usnistgov/UAS-6.0-First-Responder-UAS-Wireless-Data-Gatherer-Challenge/pics/FoxNode_disp1.jpg

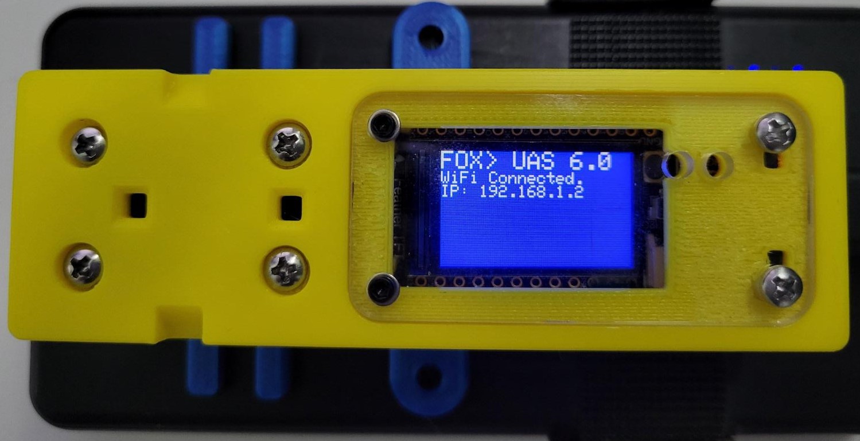
pics/FoxNode_disp1.jpg
