usnistgov/UAS-6.0-First-Responder-UAS-Wireless-Data-Gatherer-Challenge/pics/FoxNode_Fully_Connected.jpg

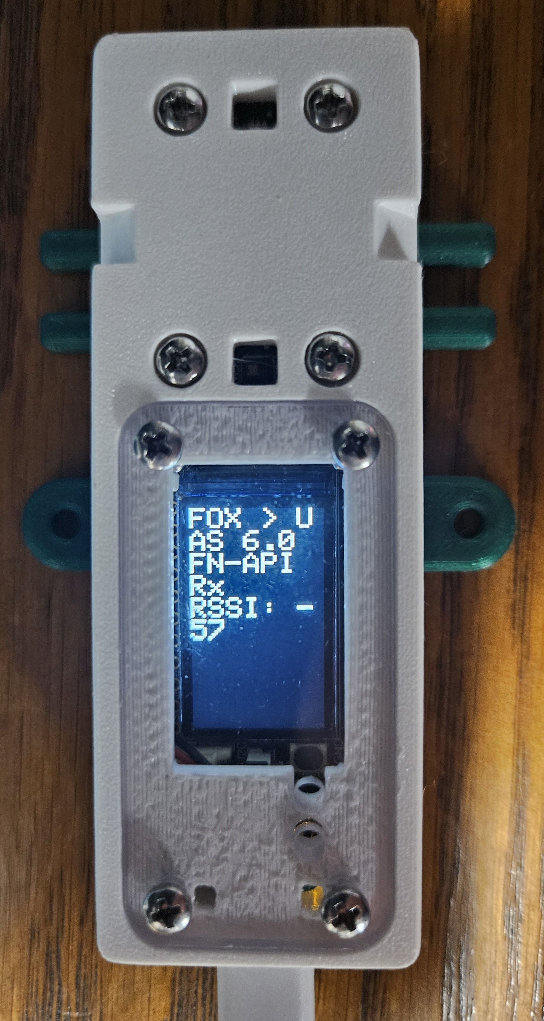
pics/FoxNode_Fully_Connected.jpg
