usnistgov/UAS-6.0-First-Responder-UAS-Wireless-Data-Gatherer-Challenge/pics/FoxNode_StateDiagram_Stage3.png

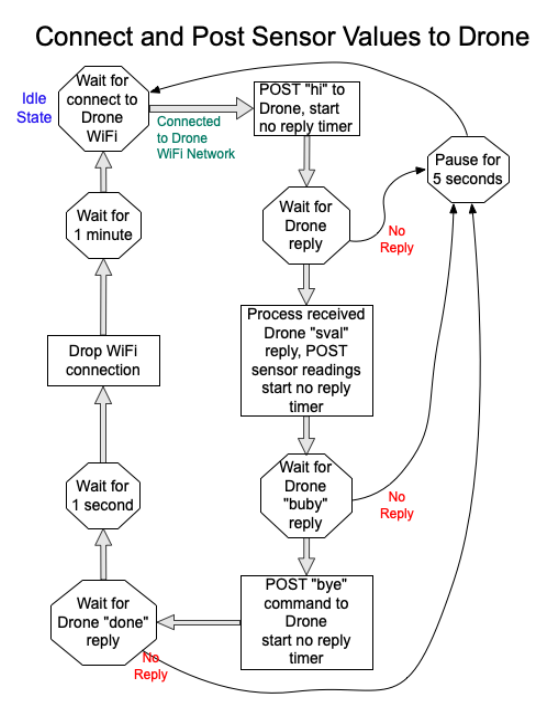
pics/FoxNode_StateDiagram_Stage3.png
