usnistgov/UAS-6.0-First-Responder-UAS-Wireless-Data-Gatherer-Challenge/stage3_foxnode/live_event_datasets/Test1/Engineering_Dynamics_Test1/Screenshot 2025-04-08 134028_ Pretty Print.png

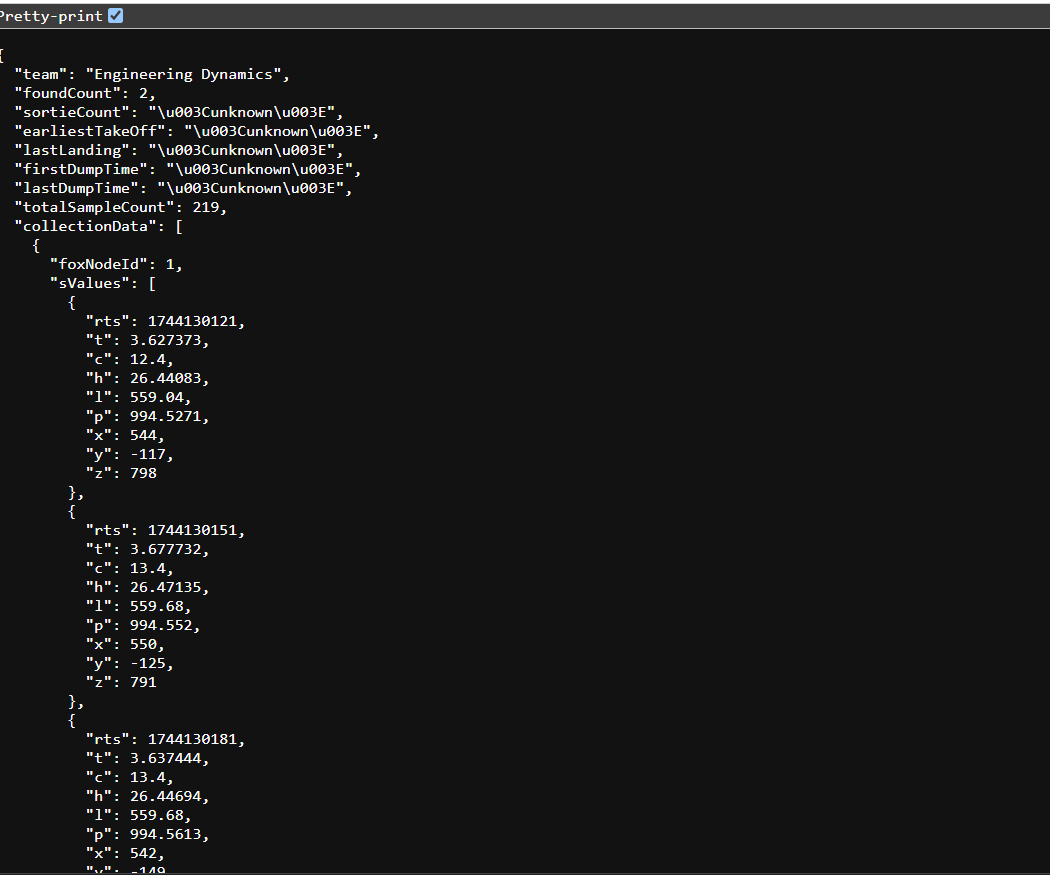
stage3_foxnode/live_event_datasets/Test1/Engineering_Dynamics_Test1/Screenshot 2025-04-08 134028_ Pretty Print.png
