usnistgov/UAS-6.0-First-Responder-UAS-Wireless-Data-Gatherer-Challenge/stage3_foxnode/live_event_datasets/Test2/Flyt_Test2/Flyt test 2.txt

{
  "bigDump": {
    "team": "Flyt",
    "foundCount": 22,
    "sortieCount": 1,
    "earliestTakeOff": 1744142474,
    "lastLanding": 1744142474,
    "firstDumpTime": 1744142475,
    "lastDumpTime": 1744144449,
    "totalSampleCount": 2008,
    "collectData": [
      {
        "foxNodeId": 5,
        "sValues": [
          {
            "t": 21.53353,
            "c": 25.7,
            "h": 37.29305,
            "l": 15892.48,
            "p": 994.1738,
            "x": 0,
            "y": 91,
            "z": 1067,
            "lat": 64.83,
            "lon": -147.77,
            "elev": 137,
            "ts": 1744142336
          },
          {
            "t": 22.27878,
            "c": 23.7,
            "h": 37.74472,
            "l": 15856.64,
            "p": 994.158,
            "x": 13,
            "y": 85,
            "z": 1015,
            "lat": 64.83,
            "lon": -147.77,
            "elev": 137,
            "ts": 1744142366
          },
          {
            "t": 22.71184,
            "c": 30.7,
            "h": 38.00717,
            "l": 15836.16,
            "p": 994.1506,
            "x": 5,
            "y": 108,
            "z": 1005,
            "lat": 64.83,
            "lon": -147.77,
            "elev": 137,
            "ts": 1744142396
          },
          {
            "t": 23.07439,
            "c": 34.7,
            "h": 38.2269,
            "l": 15897.6,
            "p": 994.1365,
            "x": -4,
            "y": 78,
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
            "lon": -85.53937,
            "elev": 226.0727,
            "ts": 3155791106
          },
          {
            "t": 9.649805,
            "c": 29.8,
            "h": 30.09079,
            "l": 1562.24,
            "p": 994.125,
            "x": -48,
            "y": -69,
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
