usnistgov/UAS-6.0-First-Responder-UAS-Wireless-Data-Gatherer-Challenge/stage3_foxnode/live_event_datasets/Test1/Flyt_Test1/Screenshot 2025-04-08 092909.png

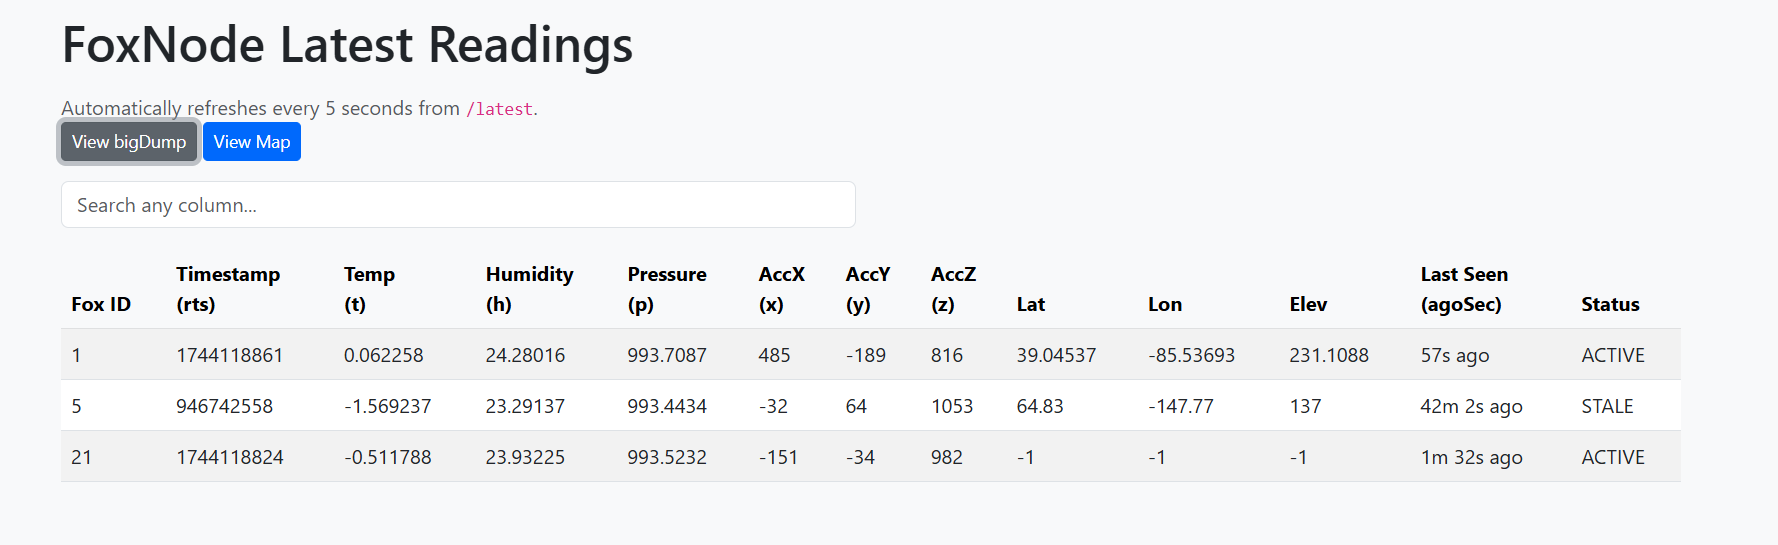
stage3_foxnode/live_event_datasets/Test1/Flyt_Test1/Screenshot 2025-04-08 092909.png
