usnistgov/UAS-6.0-First-Responder-UAS-Wireless-Data-Gatherer-Challenge/stage3_foxnode/live_event_datasets/Test1/Flyt_Test1/Test 1 bucket photos/1A.jpg

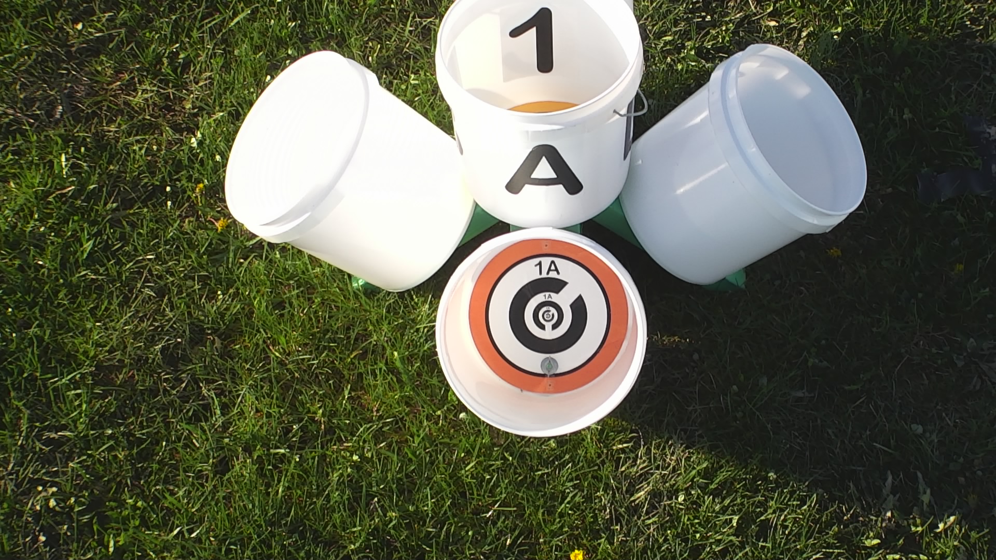
stage3_foxnode/live_event_datasets/Test1/Flyt_Test1/Test 1 bucket photos/1A.jpg
