usnistgov/UAS-6.0-First-Responder-UAS-Wireless-Data-Gatherer-Challenge/stage3_foxnode/live_event_datasets/Test1/UFRTC_Test1/Macro Map Screenshot- Patrick Request.png

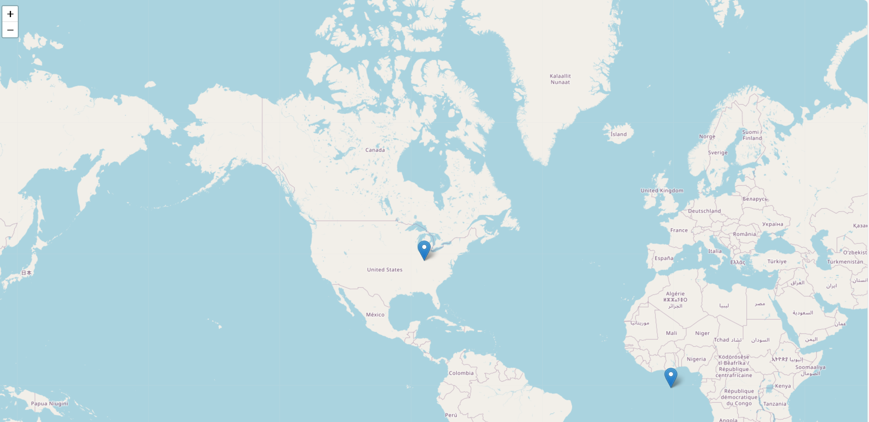
stage3_foxnode/live_event_datasets/Test1/UFRTC_Test1/Macro Map Screenshot- Patrick Request.png
