usnistgov/UAS-6.0-First-Responder-UAS-Wireless-Data-Gatherer-Challenge/stage3_foxnode/live_event_datasets/Test2/Engineering_Dynamics_Test2/NIST Server Raw.png

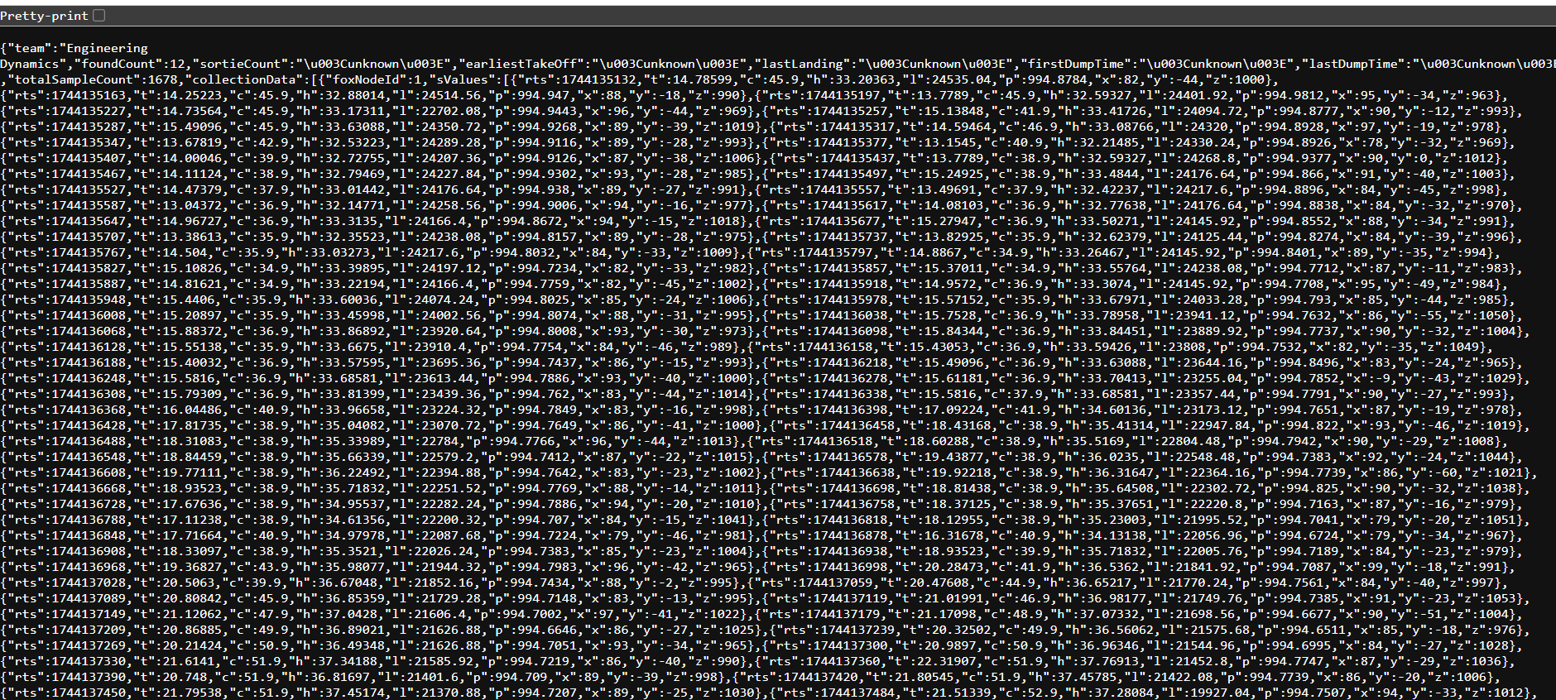
stage3_foxnode/live_event_datasets/Test2/Engineering_Dynamics_Test2/NIST Server Raw.png
