usnistgov/UAS-6.0-First-Responder-UAS-Wireless-Data-Gatherer-Challenge/stage3_foxnode/live_event_datasets/Test3/Team 7 Engineering Dynamics Test 3/RF GUI.png

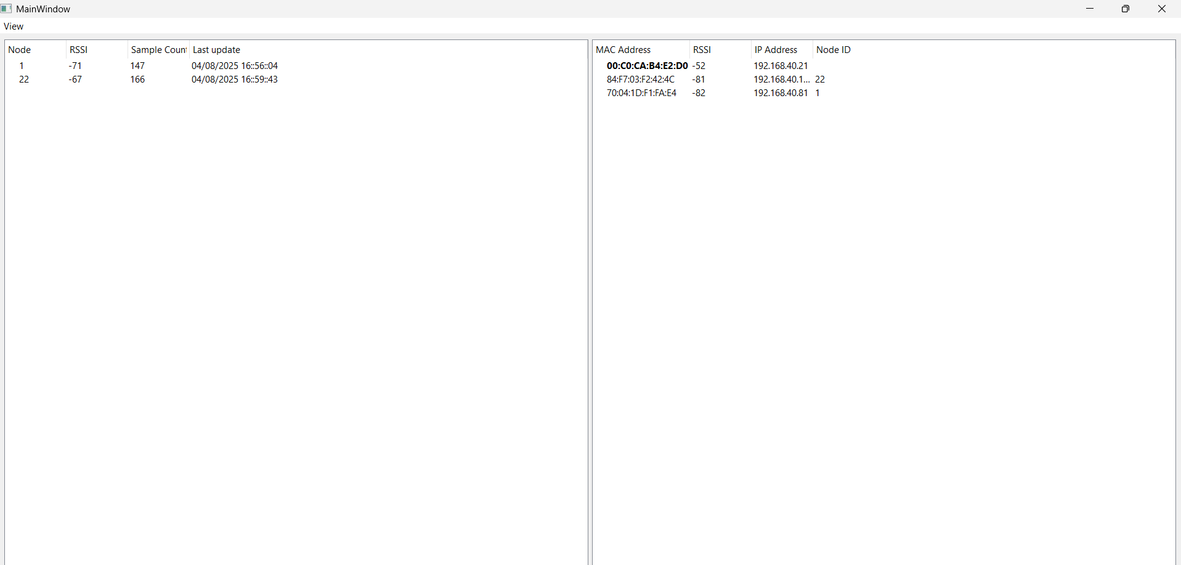
stage3_foxnode/live_event_datasets/Test3/Team 7 Engineering Dynamics Test 3/RF GUI.png
