usnistgov/UAS-6.0-First-Responder-UAS-Wireless-Data-Gatherer-Challenge/stage3_foxnode/live_event_datasets/Test4/Engineering_Dyanmics_Test4/Sensor Map.png

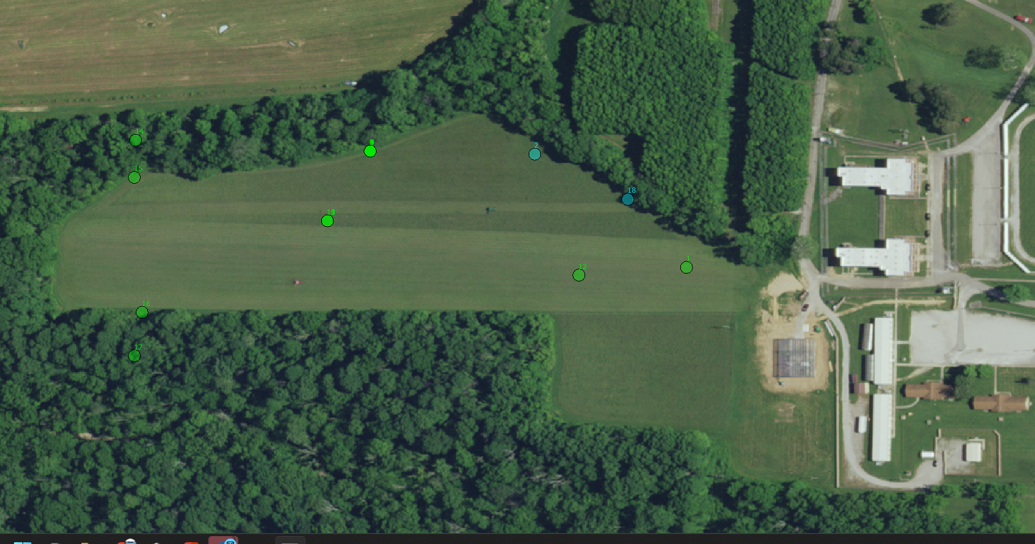
stage3_foxnode/live_event_datasets/Test4/Engineering_Dyanmics_Test4/Sensor Map.png
