usnistgov/UAS-6.0-First-Responder-UAS-Wireless-Data-Gatherer-Challenge/stage3_foxnode/live_event_datasets/Test4/Flyt_Test4/Screenshot 2025-04-09 100819.png

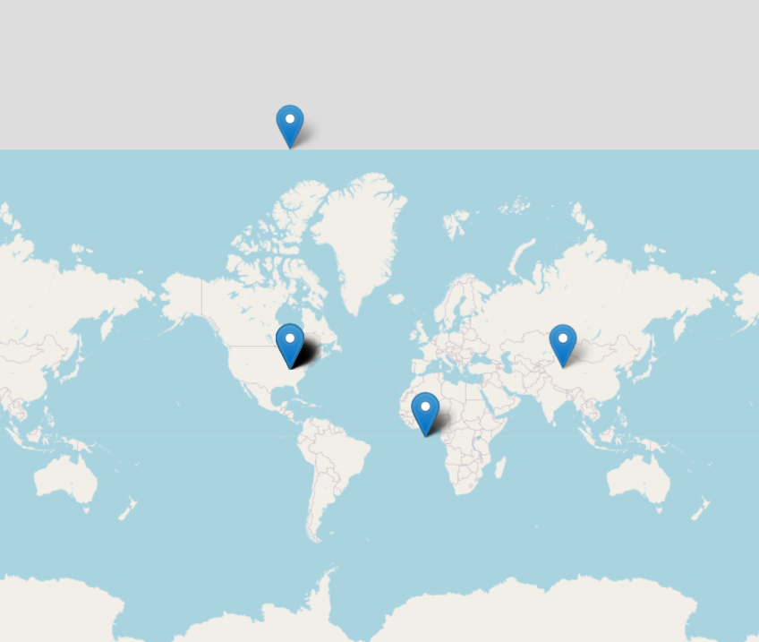
stage3_foxnode/live_event_datasets/Test4/Flyt_Test4/Screenshot 2025-04-09 100819.png
