usnistgov/UAS-6.0-First-Responder-UAS-Wireless-Data-Gatherer-Challenge/stage3_foxnode/live_event_datasets/Test4/Flyt_Test4/target_photos/DJI_0039.jpg

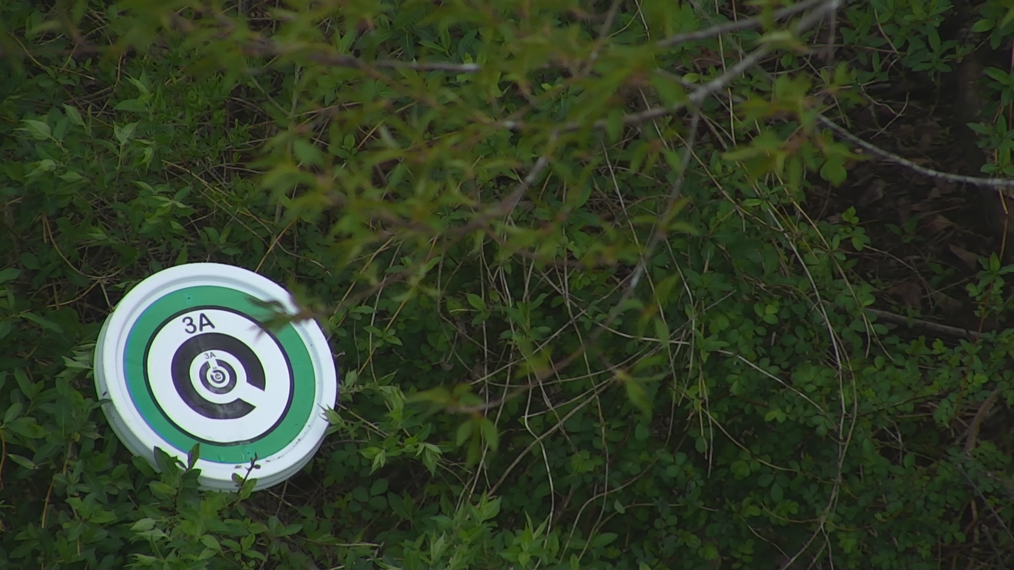
stage3_foxnode/live_event_datasets/Test4/Flyt_Test4/target_photos/DJI_0039.jpg
