usnistgov/UAS-6.0-First-Responder-UAS-Wireless-Data-Gatherer-Challenge/stage3_foxnode/live_event_datasets/Test4/UFRTC_Test4/GeoSensorData.png

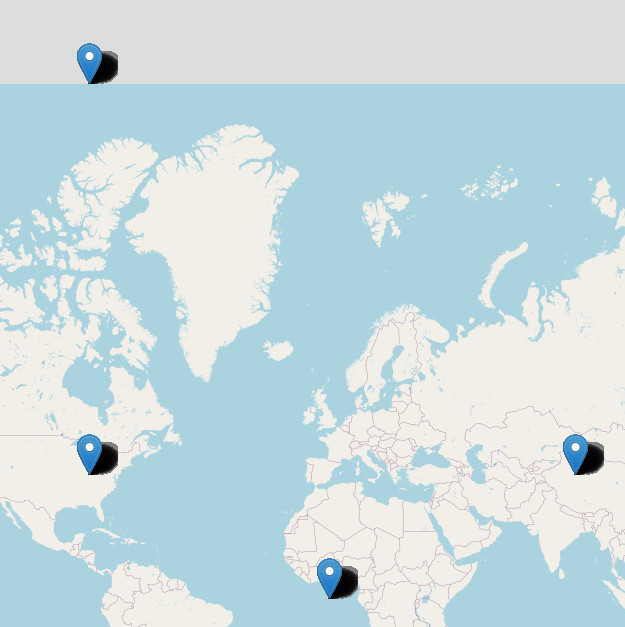
stage3_foxnode/live_event_datasets/Test4/UFRTC_Test4/GeoSensorData.png
