usnistgov/UAS-6.0-First-Responder-UAS-Wireless-Data-Gatherer-Challenge/stage3_foxnode/live_event_datasets/Test4/UFRTC_Test4/Target_Photos/DJI_20250408151507_0001_T.JPG

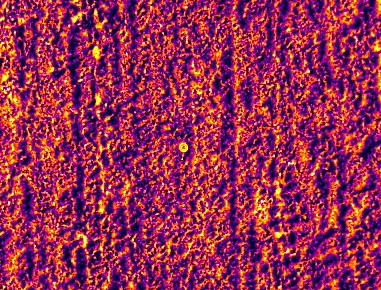
stage3_foxnode/live_event_datasets/Test4/UFRTC_Test4/Target_Photos/DJI_20250408151507_0001_T.JPG
