usnistgov/UAS-6.0-First-Responder-UAS-Wireless-Data-Gatherer-Challenge/foxnode/stateMachine/display.cpp

#include "display.h"
#include "httpComms.h"


// Compile-time guard: PSKs must never be displayed.
// If any PSK macros are present and you try to compile display.cpp, fail the build.
#if (FOXNODE_ALLOW_DISPLAY_PSK == 0)
  #if defined(WIFI_PASSWORD) || defined(NTP_WIFI_PASSWORD)
    #error "display.cpp must not reference WIFI_PASSWORD or NTP_WIFI_PASSWORD. Remove PSK display and use secrets/NVS."
  #endif
#endif

// Helper: print SSID and provisioning indicator without ever displaying PSK.
static void tftPrintSSIDLine(const char *label, WifiProfile profile) {
  String ssid;
  String throwawayPsk;  // required by secretsGetWiFi signature; do NOT display it

  bool ok = secretsGetWiFi(profile, ssid, throwawayPsk);
  tft.print(label);
  if (ok) {
    tft.print(ssid);
    tft.print("  PROV: YES");
  } else {
    tft.print("<not provisioned>  PROV: NO");
  }
  tft.println();
}

Adafruit_ST7789 tft = Adafruit_ST7789(TFT_CS, TFT_DC, TFT_RST);                          // Use dedicated hardware SPI pins for TFT disp

short disp_rotation = 3;			                                                           // Set display initial rotation TFT display: input "1" through "4"

// NOTE The RTC is on the sensor board, but this f() deals with printing.
void RTC_tftPrint() {                                                                    // TFT-display time as a formatted string (ISO 8601)
  tft.setTextSize(2);
  tft.setTextColor(ST77XX_WHITE);
  char formattedTime[20];
  snprintf(formattedTime, sizeof(formattedTime), "%04d-%02d-%02d %02d:%02d:%02d",
           myTime.tm_year + 1900, myTime.tm_mon + 1, myTime.tm_mday,
           myTime.tm_hour, myTime.tm_min, myTime.tm_sec);
  tft.println(formattedTime);
}

void tft_display(int disp_update) {
  //disp key 
  //5 - NTP Setup/Info               (YELLOW) 
  //4 - on rx HTTP update param"     (BLACK)
  //3 - on sent POST                 (GREEN)
  //2 - no connection to HTTP server (ORANGE)
  //1 - On WiFi got IP               (BLUE) 
  //0 - TFT init code                (GREEN)
  wantToPaintDisplay = 0;			// clear any pending request to paint the display
  if (disp_update == 5) {           // (YELLOW) disp FN NTP time setting 
    tft.setRotation(disp_rotation);tft.fillScreen(ST77XX_YELLOW);tft.setCursor(0, 0);
    tft.setTextSize(3);tft.setTextColor(ST77XX_WHITE);tft.println("FOX > UAS 6.0");
    tft.setTextSize(2);tft.print("FoxID: ");tft.println(thisFoxNodeId);
    tft.setTextSize(2);tft.println("NTP connect...");
    // Display SSID only (never PSK). Pulled from NVS.
    tftPrintSSIDLine("SSID: ", WifiProfile::NTP);
  } else if (disp_update == 4) {    // (BLACK) display is built in, ST7789 (TFT display) 240x135
    tft.setRotation(disp_rotation);pinMode(TFT_BACKLITE, OUTPUT);digitalWrite(TFT_BACKLITE, HIGH);tft.init(135, 240);
    tft.setCursor(0, 0);tft.fillScreen(ST77XX_BLACK);tft.setTextSize(3);tft.setTextColor(ST77XX_WHITE); // End TFT init
    tft.println("FOX > UAS 6.0");tft.println("FN-API Rx");tft.setTextSize(2);                      
  }else if (disp_update == 3) {     // (GREEN)
    tft.setRotation(disp_rotation);tft.fillScreen(ST77XX_GREEN);
    //tft.setCursor(0, 0);tft.setTextSize(2);tft.setTextColor(ST77XX_WHITE);tft.println("FOX > UAS 6.0");
    tft.setCursor(0, 0);RTC_tftPrint();  // Display formatted RTC time info
    tft.setTextSize(2);tft.setTextColor(ST77XX_RED);
    tft.print("FoxID: ");tft.println(thisFoxNodeId);
    tft.print("IP: ");tft.println(WiFi.localIP());
    tft.print("RSSI: ");tft.println(String(data_doc["rssi"]));			// This is what has been pushed to the Ringbuffer and will be POSTED when UAS connects
    tft.print("STA_TX_PWR: ");tft.println(String(data_doc["tpwr"]));
    tft.print("S:");tft.println(UAS_Server_IP);
    tft.print("HTTP Resp: ");
    if (httpResponseCode == -999) {tft.println("N/A");}
    else {tft.println(httpResponseCode);}
    tft.print("TLS: ");
    if (tlsState == TLS_STATE_OK) {
      tft.println("OK");
    } else if (tlsState == TLS_STATE_FAIL) {
      tft.println("FAIL");
      if (tlsLastError[0]) {
        // Keep it readable on the TFT by shrinking the font for the error snippet.
        tft.setTextSize(1);
        tft.println(tlsLastError);
        tft.setTextSize(2);
      }
    } else {
      tft.println("N/A");
    }

    tft.setTextColor(ST77XX_WHITE);										// Set back to white for later calls
  } else if (disp_update == 2) {      // (ORANGE) no WiFi/HTTP Server connection available 
    tft.setRotation(disp_rotation);tft.fillScreen(ST77XX_ORANGE);tft.setCursor(0, 0);tft.setTextSize(3);tft.setTextColor(ST77XX_WHITE);
    tft.println(("FOX > UAS 6.0"));tft.setTextSize(2);
    RTC_tftPrint();
    tft.print("FoxID: ");tft.println(thisFoxNodeId);
    tft.println("Looking for Network");
    // Display SSID only (never PSK). Pulled from NVS.
    tftPrintSSIDLine("SSID: ", WifiProfile::UAS6);
    tft.println(UAS_Server_IP);
  } else if (disp_update == 1) {     // (BLUE) disp IP connected
    tft.setRotation(disp_rotation);tft.fillScreen(ST77XX_BLUE);tft.setCursor(0, 0);tft.setTextSize(3);tft.setTextColor(ST77XX_WHITE);
    tft.println("FOX > UAS 6.0");tft.setTextSize(2);
    RTC_tftPrint();  // Display formatted RTC time info
    tft.print("FoxID: ");tft.println(thisFoxNodeId);
    tft.println("WiFi Connected.");
    tft.print("IP: ");tft.println(WiFi.localIP());
    tft.print("RSSI: ");tft.println(String(WiFi.RSSI()));
  } else if (disp_update == 0) {    // (GREEN) disp initial setup  screen
    tft.init(135, 240);pinMode(TFT_BACKLITE, OUTPUT);digitalWrite(TFT_BACKLITE, HIGH);    // Start TFT &turn on backlite
    tft.setRotation(disp_rotation);tft.setCursor(0, 0);tft.fillScreen(ST77XX_GREEN);tft.setTextSize(3);
    tft.setTextColor(ST77XX_WHITE);tft.println("FOX > UAS 6.0");
    tft.println("INITIALIZED");tft.setTextSize(2);						// End TFT init
  } else {                                                                              
    Serial.println("Error in display function...");
    Serial.println("tft_display(");
    Serial.println(disp_update, DEC);
    Serial.print(")");
  }
}
