usnistgov/UAS-6.0-First-Responder-UAS-Wireless-Data-Gatherer-Challenge/foxnode/stateMachine/display.h

#ifndef DISPLAY_H
#define DISPLAY_H

// SCOPE: globals for code that writes things to the onboard ESP display (TFT)

// Includes
#include <Arduino.h>
#include <Adafruit_GFX.h>                                        // Display hardware def.
#include <Adafruit_ST7789.h>                                     // Hardware-specific library for ST7789
#include "serial.h"
#include "sensor.h"                                              // JSON lib
#include "state.h"                                               // for UAS_Server var
#include "secrets.h"                                             // NVS secrets

// ===========================
// Display Security Guardrails
// ===========================
// Never display PSKs on the TFT. If you *intentionally* want to override this for lab bring-up,
// you must set FOXNODE_ALLOW_DISPLAY_PSK to 1 *in your build flags* (not in source).
#ifndef FOXNODE_ALLOW_DISPLAY_PSK
#define FOXNODE_ALLOW_DISPLAY_PSK 0
#endif


// Global Variables
extern Adafruit_ST7789 tft;
extern short disp_rotation;
extern unsigned int wantToPaintDisplay;

// Function Declarations
extern void RTC_tftPrint();			
extern void initializeDisplay(void);
extern void tft_display(int disp_update);

void RTC_tftPrint();

#endif  // DISPLAY_H
